PokaInc/talko-lingo/docs/img/gcode.jpg

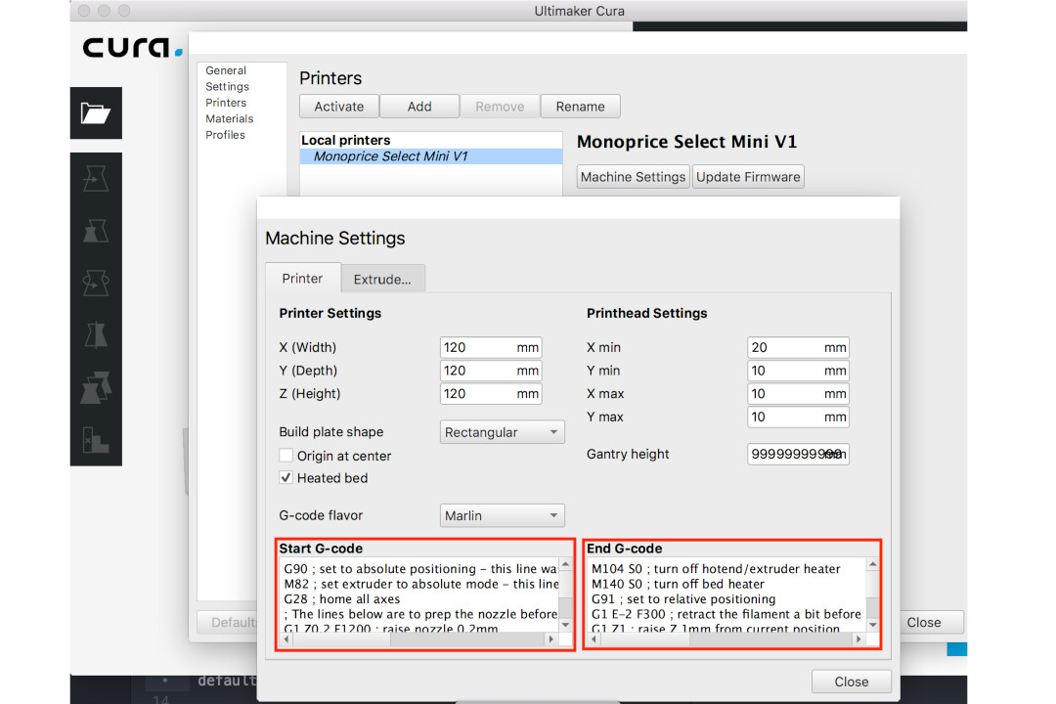
docs/img/gcode.jpg
