PokaInc/talko-lingo/website/images/speak-no-evil-monkey.png

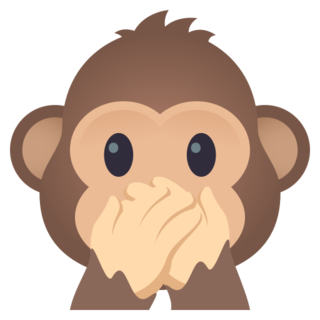
website/images/speak-no-evil-monkey.png
